DavesKosmoModules/Buren-Mult/Docs/20211023_091158.jpg

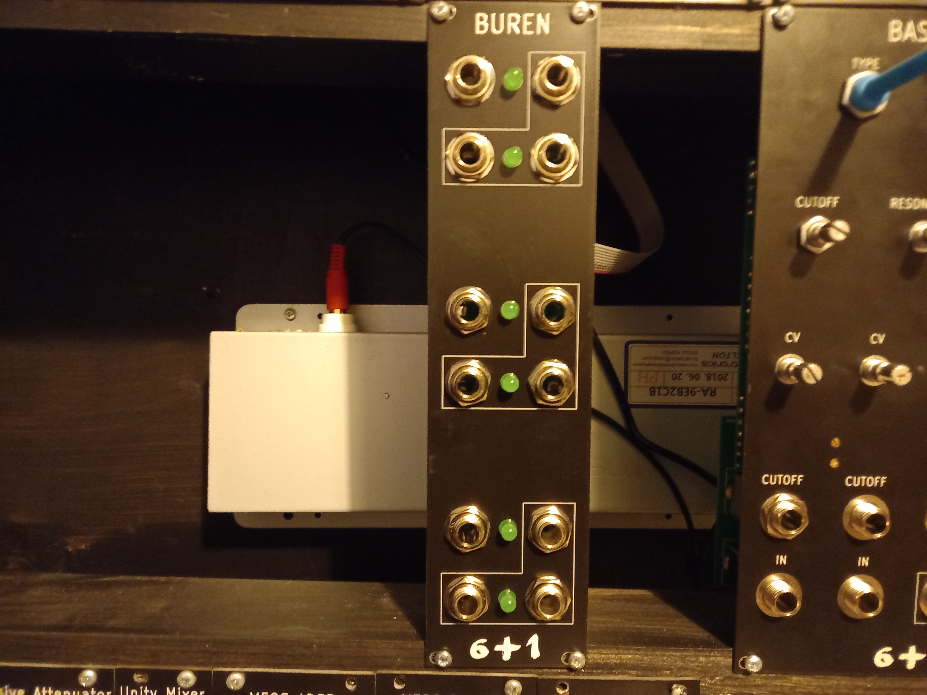
Docs/20211023_091158.jpg
